DisruptivelyUseful/Trash-Printer/Build Files - STL/Trash Printer V3 - Z Motor Bracket.stl

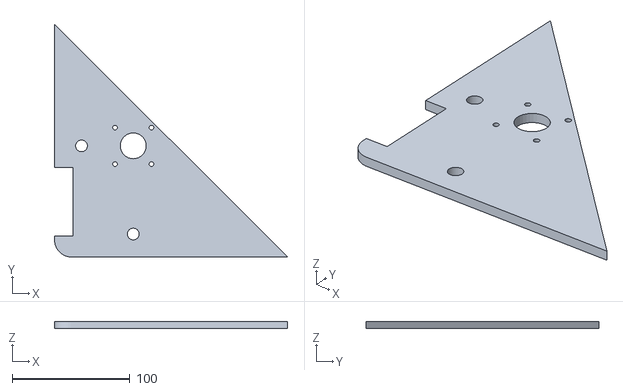
[picture p15: CAD file, 2022-06-12]
Build Files - STL/Trash Printer V3 - Z Motor Bracket.stl
198.2 x 198.2 x 6.35
